mesotokyo/fow/spice_data/ef01.asc

C1: cap; 10µ
C2: cap; 10µ
C3: cap; 33p
C4: cap; 200n
C5: cap; 0.1µ
C6: cap; 0.1µ
C7: cap; 0.1µ
C8: cap; 0.1µ
C11: cap; 0.1µ
C12: cap; 22µ
C13: cap; 22µ
D1: diode
D2: diode
D3: diode
D4: LED
D5: LED
D6: diode
D7: diode
Q1: npn; 2N3904
Q2: npn; 2N3904
Q3: npn; 2N3904
R1: res; 4.7k
R2: res; 2k
R3: res; 100
R4: res; 470
R5: res; {env_lv}
R6: res; 10k
R7: res; 1Meg
R8: res; {gain}
R9: res; 10k
R10: res; 10k
R11: res; {sens}
R12: res; 100
R13: res; {thr_r}
R14: res; {thr_l}
R15: res; 100
R16: res; {release}
R17: res; 4.7k
R18: res; {buf_lv}
R19: res; 1k
R20: res; 2k
R21: res; 4.7k
R22: res; 1Meg
R23: res; 20
R24: res; 47k
R25: res; 100k
R26: res; 100k
R27: res; 100k
R28: res; 22
R29: res; 22
R30: res; 1k
R31: res; 100
U1: LT1058A
U2: LT1058A
U3: LT1058A
U4: LT1058A
U5: LT1058A
U6: LT1058A
U7: LT1058A
U8: LT1058A
V1: voltage; 12
V2: voltage; 12
V3: voltage; wavefile=sample.wav; AC 1 0
X1: lcr-0203
Named nets: 0, -12V, +12V, signal, envelop, gate, buffered_out
.tran 800m
;.ac oct 100 10 40k
.param gain 7*4.7k
.param sens 5k
.param env_lv 1k
;.step param env_lv list 1 300 1k
.param buf_lv 1k
.param threshold 0.8
;.step param threshold list 0 0.2 0.4 0.6 0.8 1
.param thr_l (1-{threshold})*1k+1
.param thr_r ({threshold})*1k+1
.param release 250k
sens:B10k
gain:A1M
threshold:1k
envelop_sens:A1k
buf_lv:2k
release:500k
